ViniciusTxc3/Hardware_Software_Control_Prosthesis/datasheets/CIs/ADUM1250_example.png

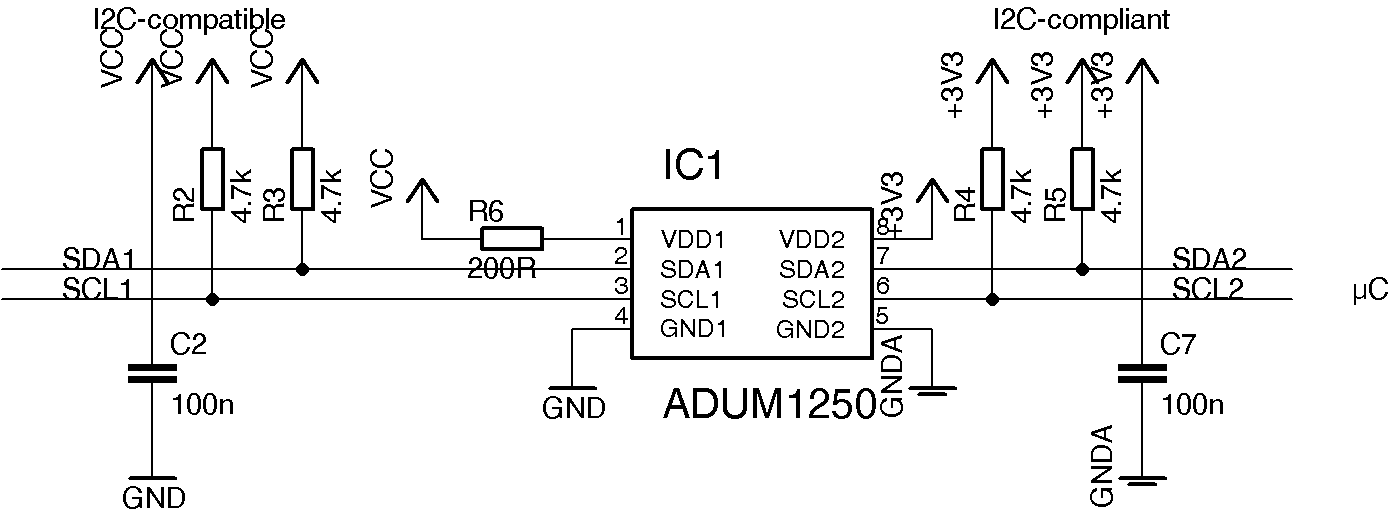
datasheets/CIs/ADUM1250_example.png
