ViniciusTxc3/Hardware_Software_Control_Prosthesis/datasheets/CIs/voltage_charge.jpg

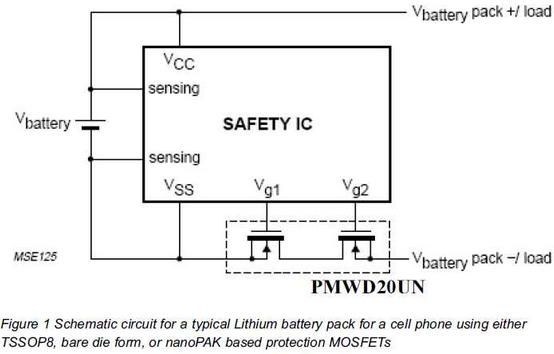
datasheets/CIs/voltage_charge.jpg
