ViniciusTxc3/Hardware_Software_Control_Prosthesis/datasheets/Diodo Zener/Circuit_3_Reverse_Battery_Protection_N-MOSFET.jpg

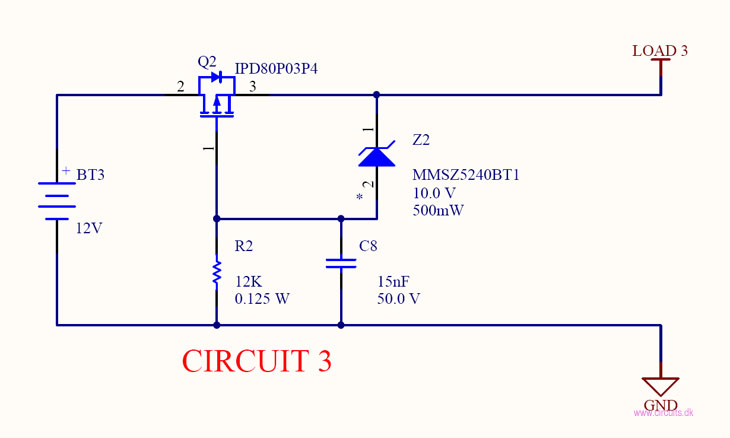
datasheets/Diodo Zener/Circuit_3_Reverse_Battery_Protection_N-MOSFET.jpg
