ViniciusTxc3/Hardware_Software_Control_Prosthesis/datasheets/PIC - DSPIC33FJ32MC202/dspic33fj32mc202_circuit11.png

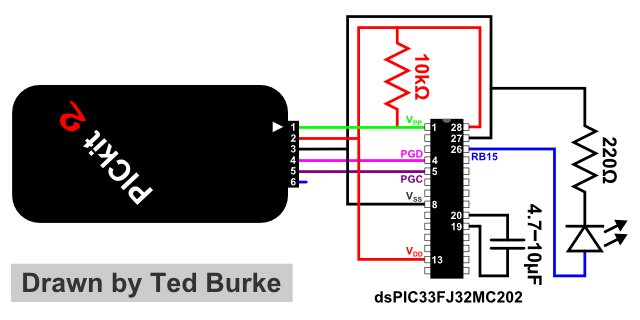
datasheets/PIC - DSPIC33FJ32MC202/dspic33fj32mc202_circuit11.png
